keebio/quefrency-case/rev2/Top Shell - Right 60.stl

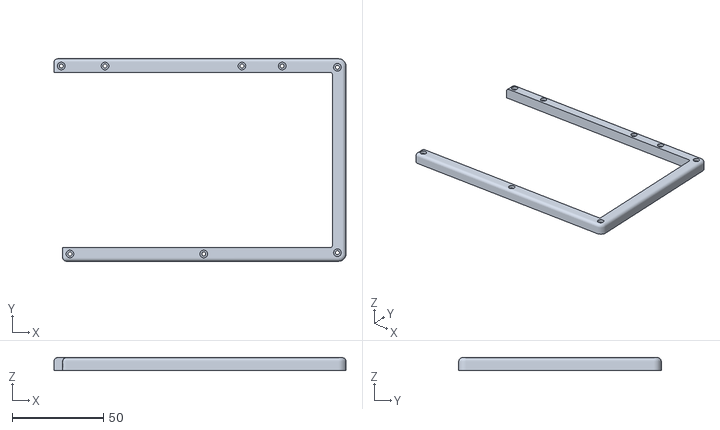
[picture p15: CAD file, 2020-12-21]
rev2/Top Shell - Right 60.stl
160.4 x 111.2 x 7.00
