keebio/quefrency-case/enclosed-case/Rev. 2/Mid Layer - Right 60 for Rev. 2.stl

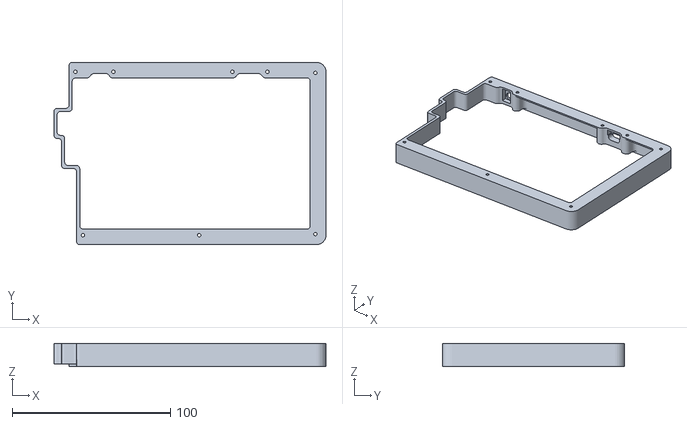
[picture p16: CAD file, 2022-01-09]
enclosed-case/Rev. 2/Mid Layer - Right 60 for Rev. 2.stl
171.9 x 115.2 x 14.8
