keebio/quefrency-case/enclosed-case/Top Shell - Right 65.stl

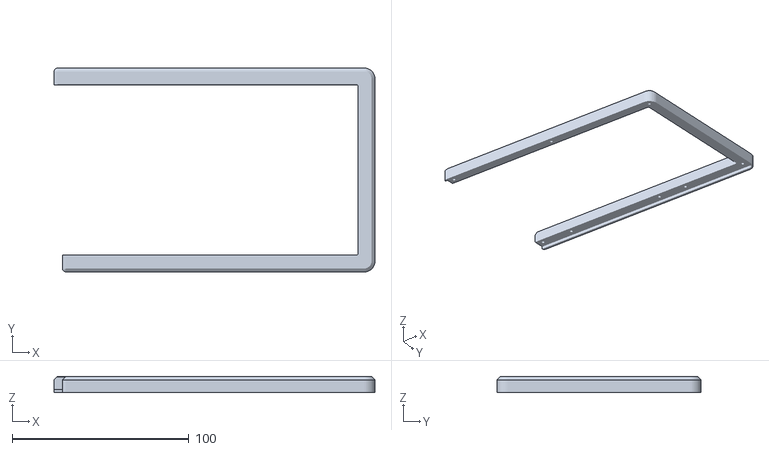
[picture p17: CAD file, 2024-10-10]
enclosed-case/Top Shell - Right 65.stl
181.4 x 115.2 x 9.30
