keebio/quefrency-case/rev2/Top Shell - Right 65.stl

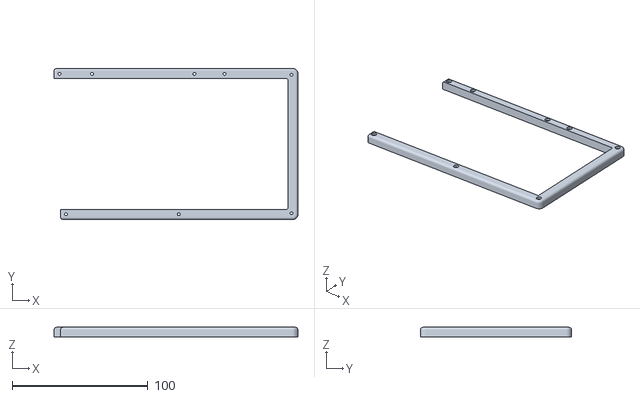
[picture p18: CAD file, 2020-12-21]
rev2/Top Shell - Right 65.stl
179.4 x 111.2 x 7.00
