keebio/quefrency-case/enclosed-case/Mid Layer - Rev. 6 - Left No Macro.stl

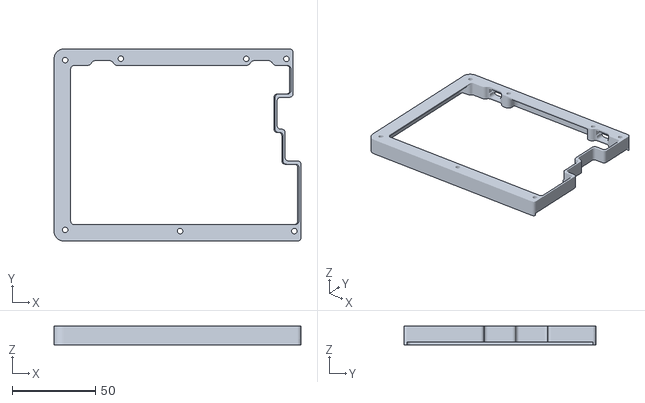
[picture p19: CAD file, 2024-10-10]
enclosed-case/Mid Layer - Rev. 6 - Left No Macro.stl
148.1 x 115.3 x 11.3
