keebio/quefrency-case/enclosed-case/Mid Layer - Rev. 6 - Left Macro.stl

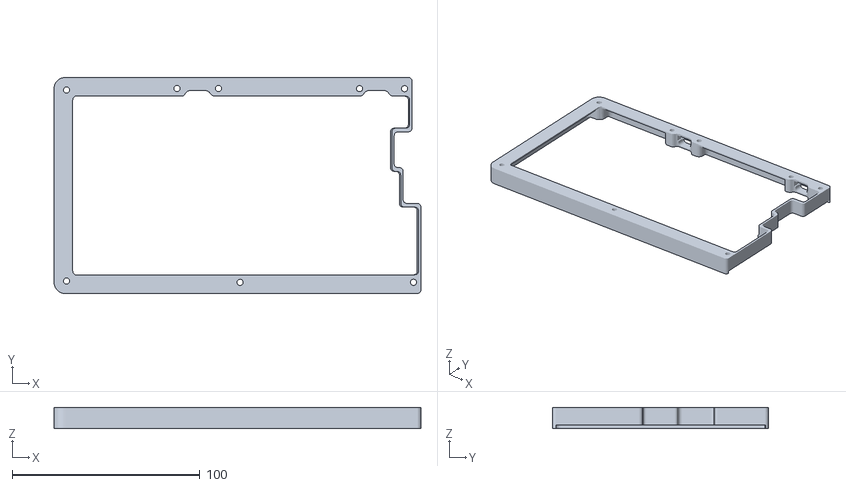
[picture p20: CAD file, 2024-10-10]
enclosed-case/Mid Layer - Rev. 6 - Left Macro.stl
195.7 x 115.3 x 11.3
