keebio/quefrency-case/rev2/bottom-plate-left-macro.dxf

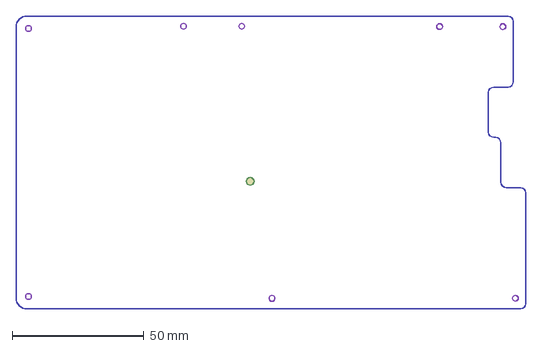
[picture p21: CAD file, 2020-08-25]
rev2/bottom-plate-left-macro.dxf
193.7 x 111.2 mm
