keebio/quefrency-case/rev2/bottom-plate-right.dxf

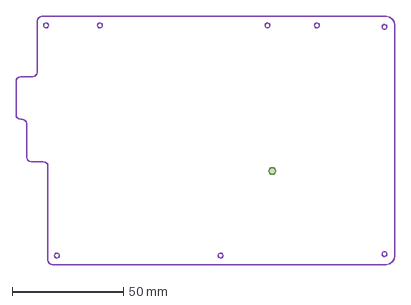
[picture p22: CAD file, 2020-08-25]
rev2/bottom-plate-right.dxf
169.9 x 111.2 mm
