keebio/quefrency-case/rev2/bottom-plate-left.dxf

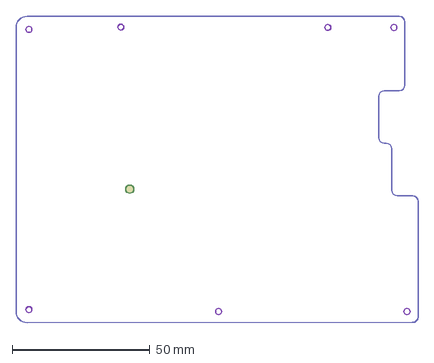
[picture p23: CAD file, 2020-08-25]
rev2/bottom-plate-left.dxf
146.1 x 111.3 mm
