keebio/quefrency-case/enclosed-case/Filleted Top Shells/Top Shell - Left Macro with Encoder.stl

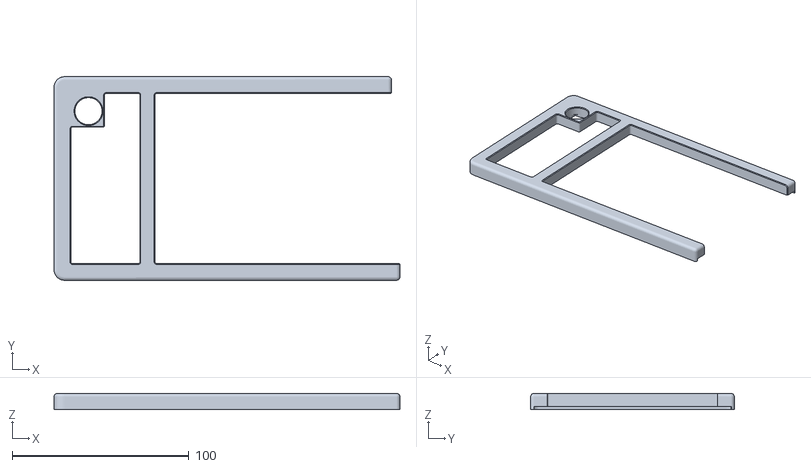
[picture p24: CAD file, 2021-10-22]
enclosed-case/Filleted Top Shells/Top Shell - Left Macro with Encoder.stl
195.7 x 115.3 x 9.30
