keebio/quefrency-case/rev2/bottom-plate-right-65.dxf

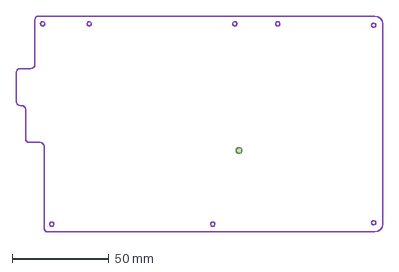
[picture p25: CAD file, 2020-08-25]
rev2/bottom-plate-right-65.dxf
189.0 x 111.2 mm
