keebio/quefrency-case/enclosed-case/Filleted Top Shells/Top Shell - Right 65 for Rev. 4 Proto.stl

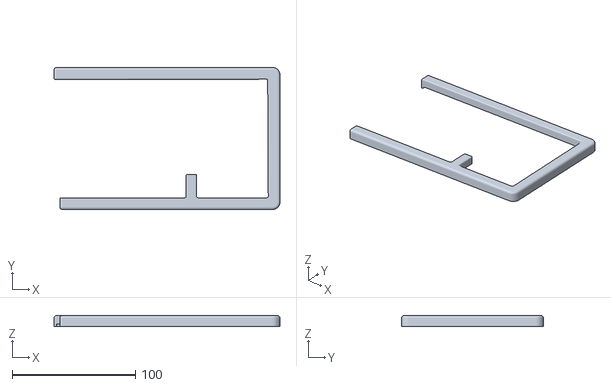
[picture p27: CAD file, 2021-08-13]
enclosed-case/Filleted Top Shells/Top Shell - Right 65 for Rev. 4 Proto.stl
183.4 x 115.2 x 8.80
