keebio/quefrency-case/enclosed-case/Mid Layer - Rev. 3-6 - Right 60.stl

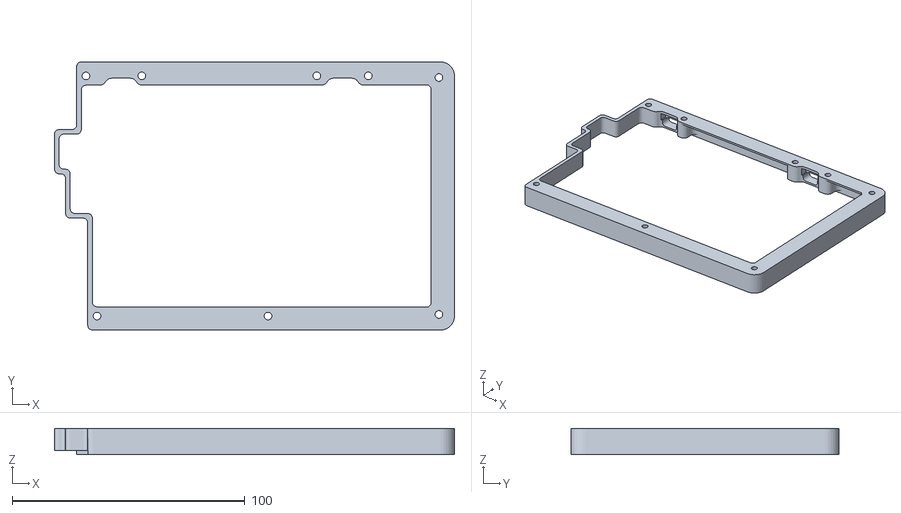
[picture p28: CAD file, 2022-04-06]
enclosed-case/Mid Layer - Rev. 3-6 - Right 60.stl
171.9 x 115.2 x 11.3
