keebio/quefrency-case/enclosed-case/Bottom Wedge - Left Macro.stl

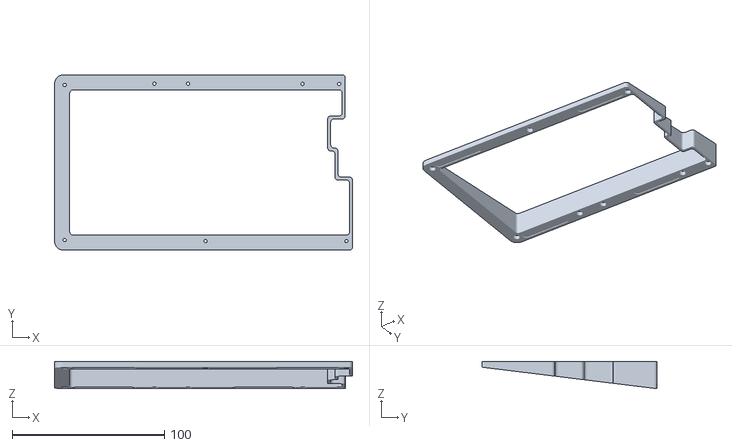
[picture p29: CAD file, 2022-02-07]
enclosed-case/Bottom Wedge - Left Macro.stl
195.7 x 115.3 x 18.0
