keebio/quefrency-case/enclosed-case/Bottom Wedge - Left No Macro.stl

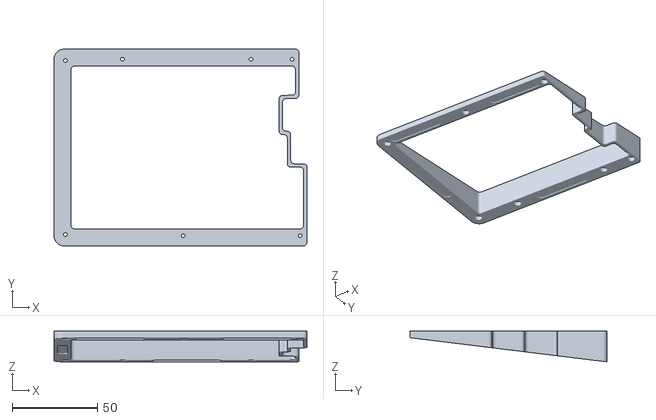
[picture p30: CAD file, 2022-02-07]
enclosed-case/Bottom Wedge - Left No Macro.stl
148.1 x 115.3 x 18.0
