keebio/quefrency-case/rev2/Mid - Left 60.stl

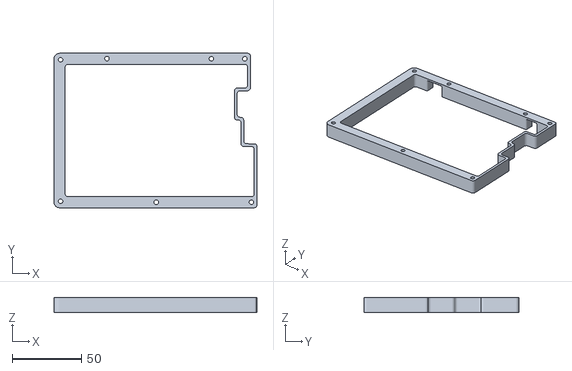
[picture p31: CAD file, 2020-07-24]
rev2/Mid - Left 60.stl
146.1 x 111.3 x 11.0
