keebio/quefrency-case/enclosed-case/Bottom Wedge - Right 60.stl

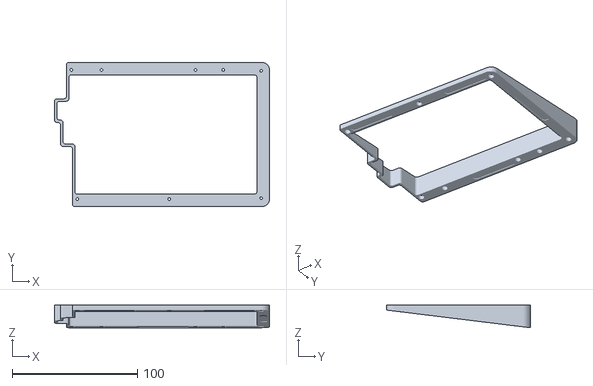
[picture p32: CAD file, 2022-02-07]
enclosed-case/Bottom Wedge - Right 60.stl
171.9 x 115.2 x 18.0
