keebio/quefrency-case/rev2/Mid - Right 65.stl

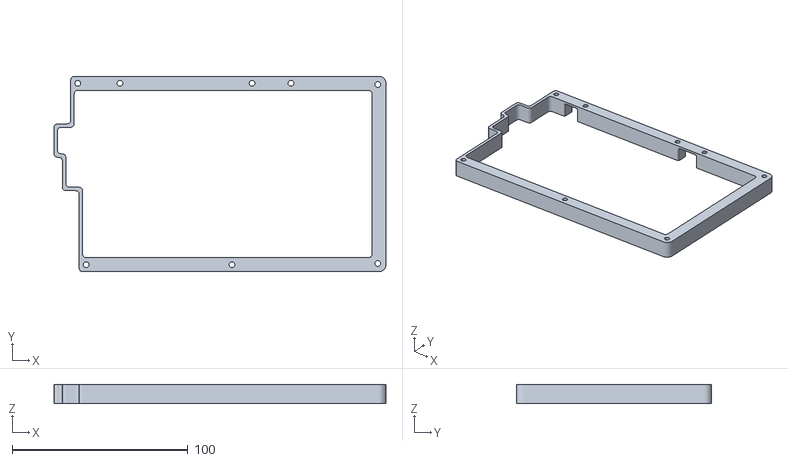
[picture p33: CAD file, 2020-07-24]
rev2/Mid - Right 65.stl
189.0 x 111.2 x 11.0
