keebio/quefrency-case/enclosed-case/Bottom Wedge - Right 65.stl

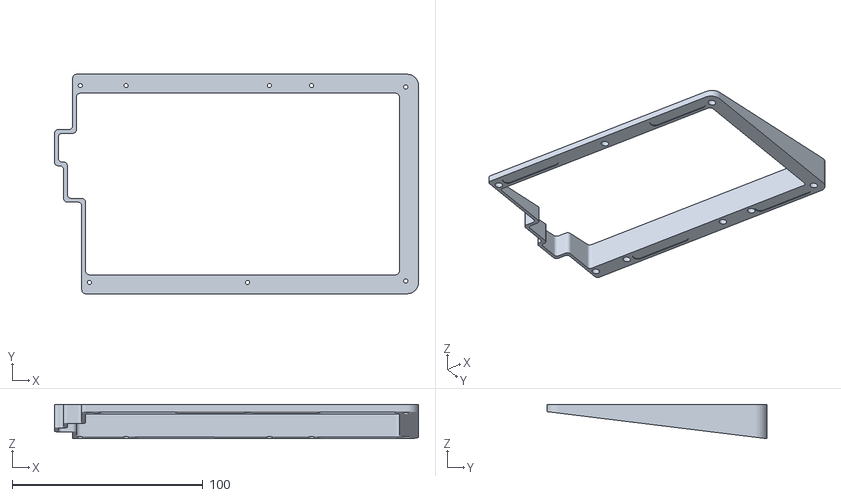
[picture p34: CAD file, 2022-02-07]
enclosed-case/Bottom Wedge - Right 65.stl
191.0 x 115.2 x 18.0
