keebio/quefrency-case/rev2/Mid - Right 60.stl

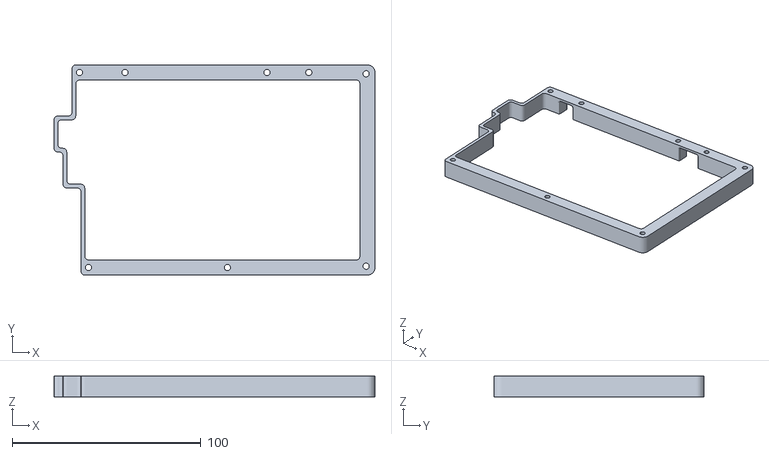
[picture p35: CAD file, 2020-07-24]
rev2/Mid - Right 60.stl
169.9 x 111.2 x 11.0
