keebio/quefrency-case/enclosed-case/Mid Layer - Rev. 3-6 - Right 65 Tenting.stl

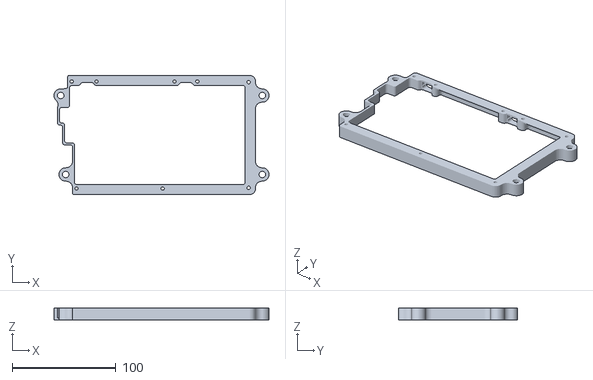
[picture p36: CAD file, 2021-09-18]
enclosed-case/Mid Layer - Rev. 3-6 - Right 65 Tenting.stl
207.4 x 115.2 x 11.3
