keebio/quefrency-case/rev2/Mid - Left Macro.stl

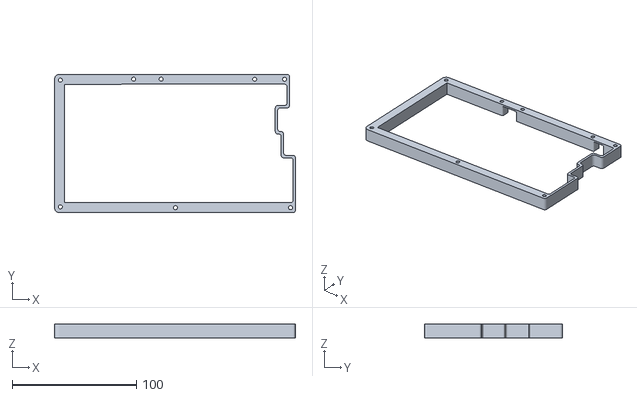
[picture p37: CAD file, 2020-07-24]
rev2/Mid - Left Macro.stl
193.7 x 111.2 x 11.0
