keebio/quefrency-case/enclosed-case/Mid Layer - Rev. 3-5 - Left Macro Tenting.stl

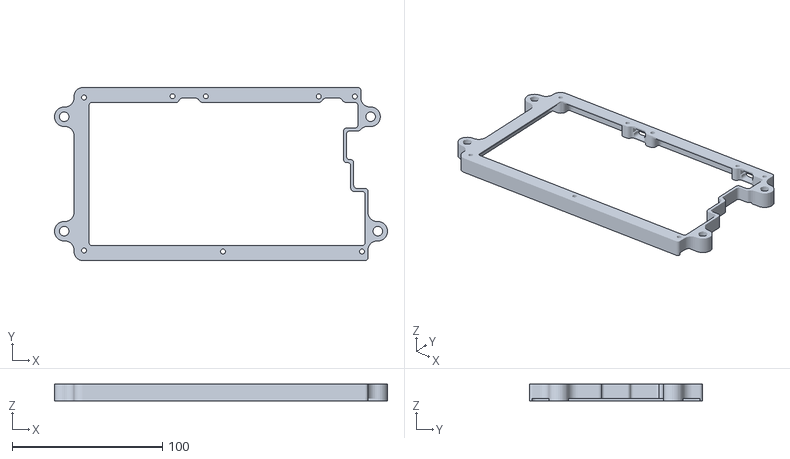
[picture p38: CAD file, 2021-09-18]
enclosed-case/Mid Layer - Rev. 3-5 - Left Macro Tenting.stl
221.7 x 115.3 x 11.3
