keebio/quefrency-case/enclosed-case/Mid Layer - Rev. 3-5 - Left No Macro Tenting.stl

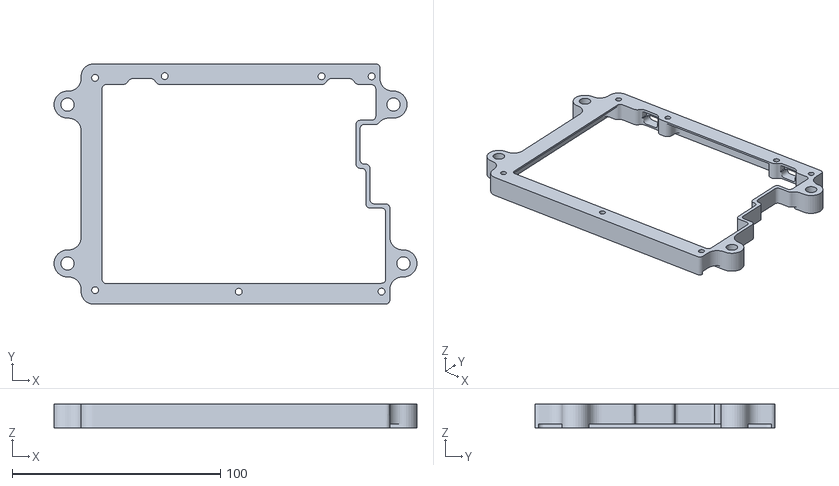
[picture p39: CAD file, 2021-09-18]
enclosed-case/Mid Layer - Rev. 3-5 - Left No Macro Tenting.stl
174.1 x 115.3 x 11.3
