keebio/quefrency-case/enclosed-case/Mid Layer - Rev. 3-6 - Right 65.stl

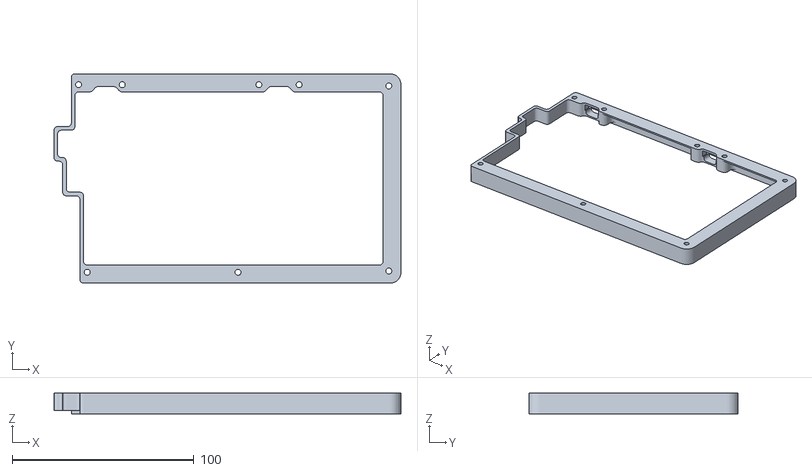
[picture p40: CAD file, 2021-08-12]
enclosed-case/Mid Layer - Rev. 3-6 - Right 65.stl
191.0 x 115.2 x 11.3
